GNB-UAM/UAMSense/UAMSense1/sensors_3d.jpg

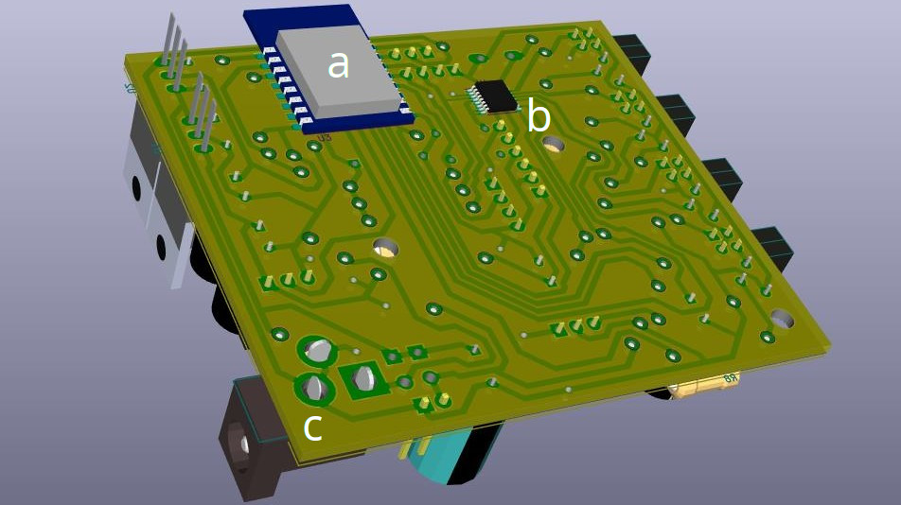
UAMSense1/sensors_3d.jpg
