GNB-UAM/UAMSense/UAMSense1/sensors_pcb.png

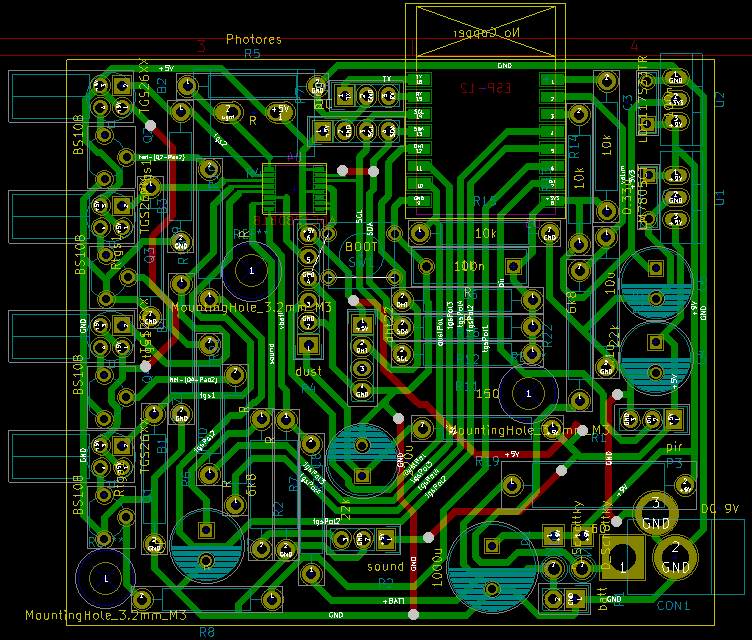
UAMSense1/sensors_pcb.png
