GNB-UAM/UAMSense/UAMSense2/uamsense2_pcb.png

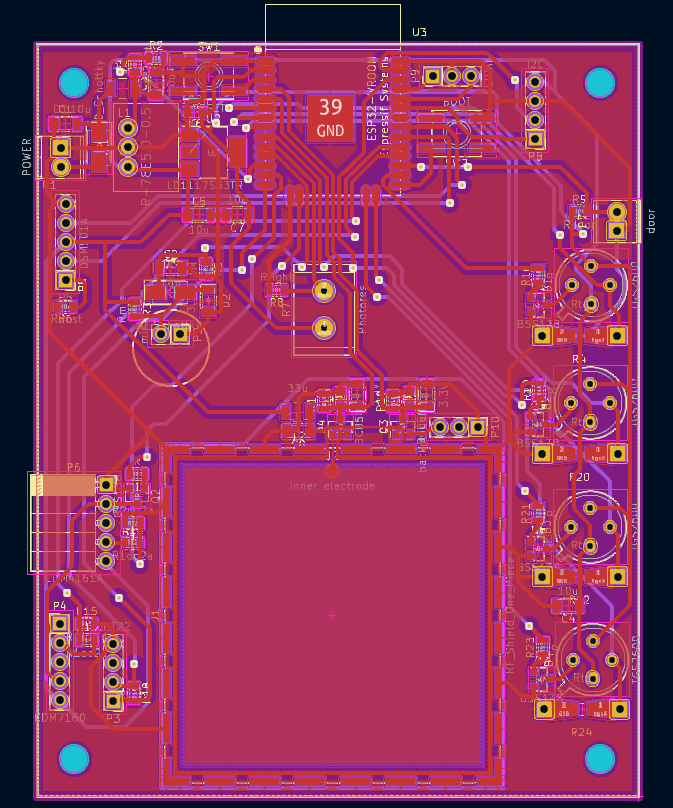
UAMSense2/uamsense2_pcb.png
