GNB-UAM/UAMSense/UAMSense3/2017-07-22 03.41.13.jpg

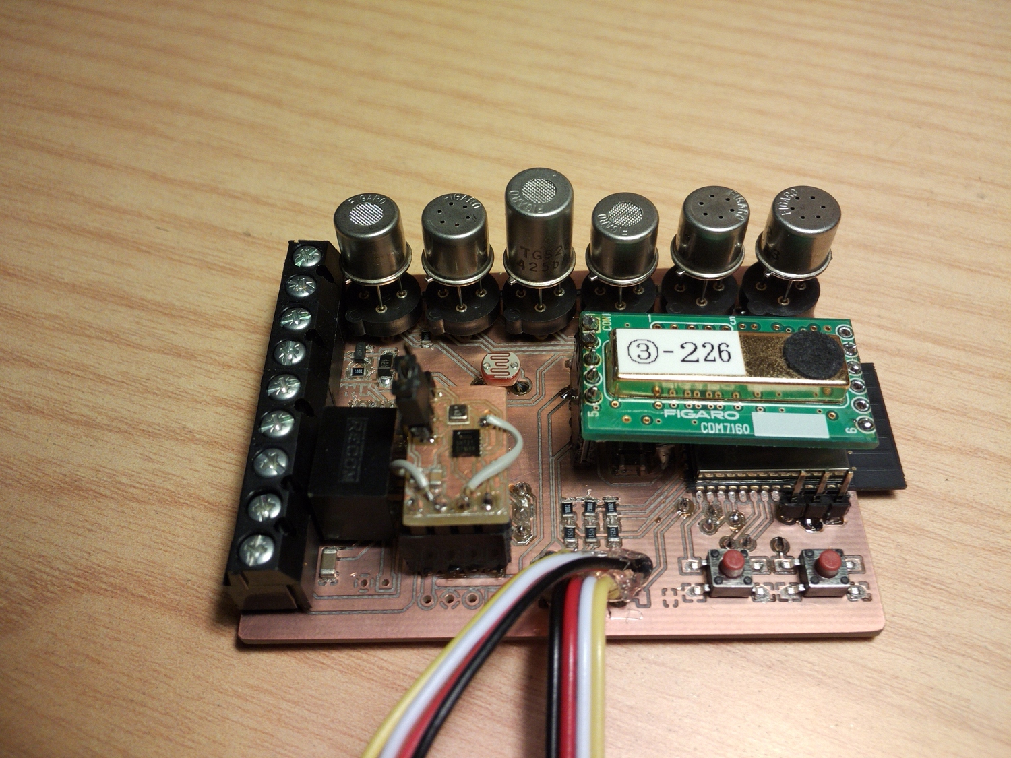
UAMSense3/2017-07-22 03.41.13.jpg
