GNB-UAM/UAMSense/UAMSense3/uamsense3_pcb.png

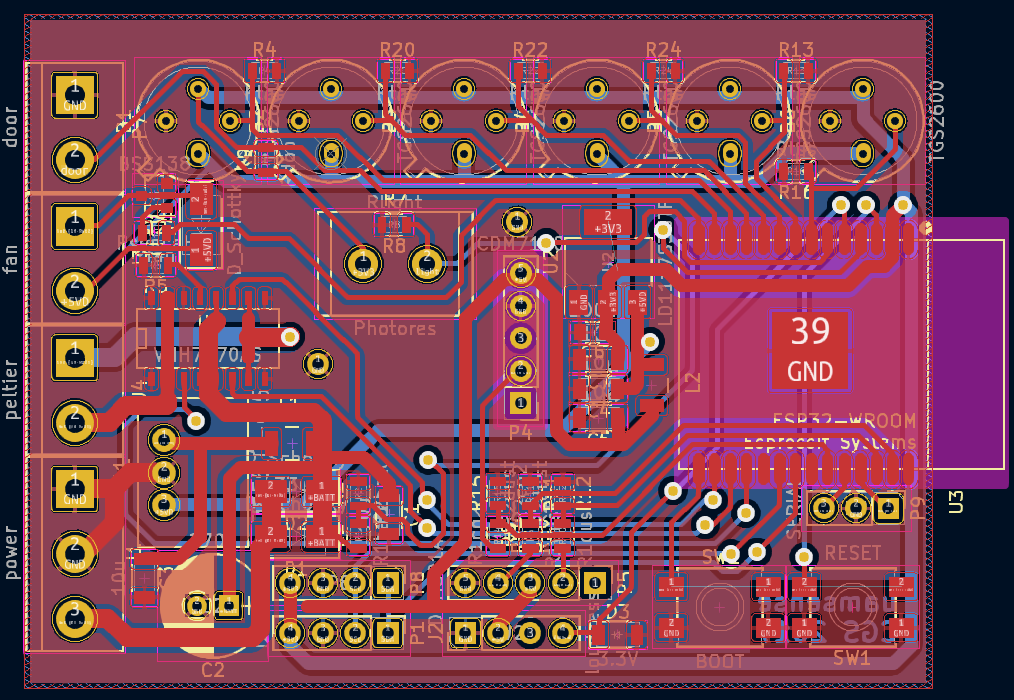
UAMSense3/uamsense3_pcb.png
