GNB-UAM/UAMSense/UAMSense4/IMG20211211204609.jpg

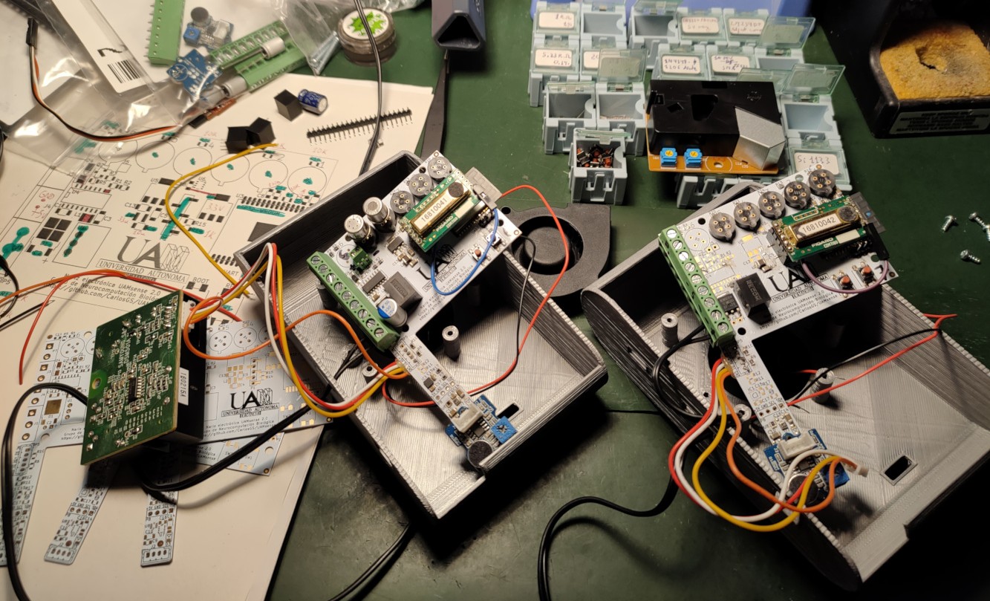
UAMSense4/IMG20211211204609.jpg
