GNB-UAM/UAMSense/UAMSense4/3Dprinted_enclosure/enclosurePrinted.jpg

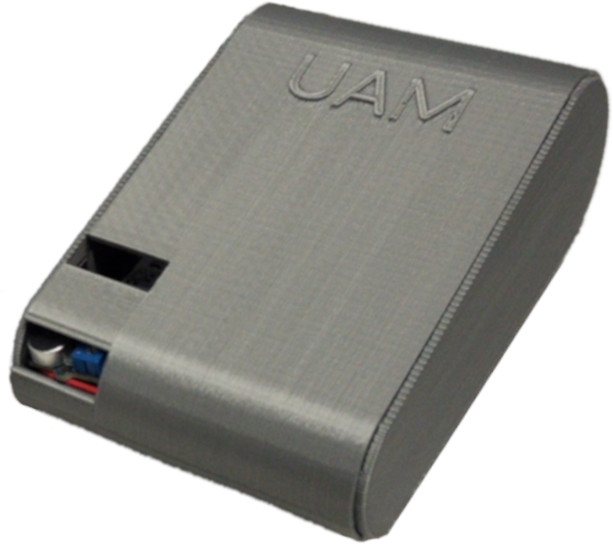
UAMSense4/3Dprinted_enclosure/enclosurePrinted.jpg
